petl/Helmet_blinker/Photos/IMG_20210405_172852.jpg

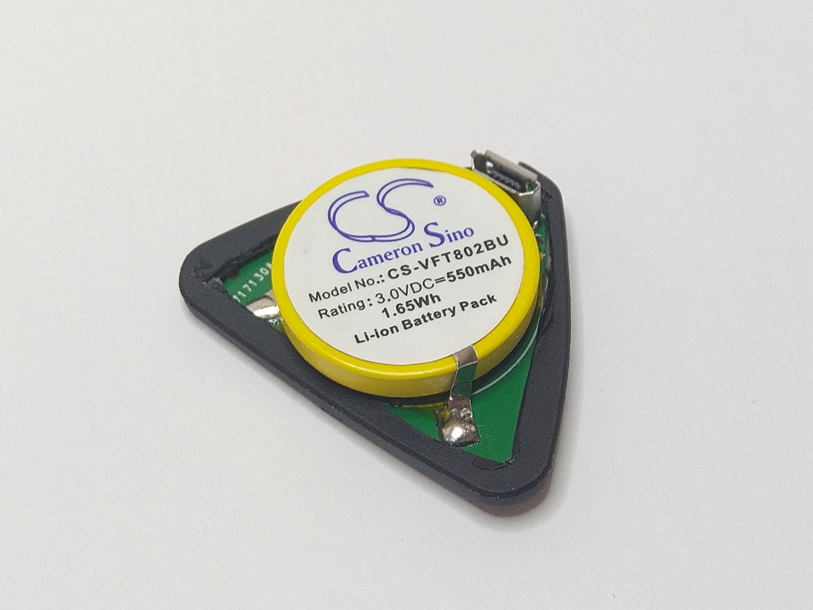
Photos/IMG_20210405_172852.jpg
