petl/Helmet_blinker/Photos/IMG_20210405_173359.jpg

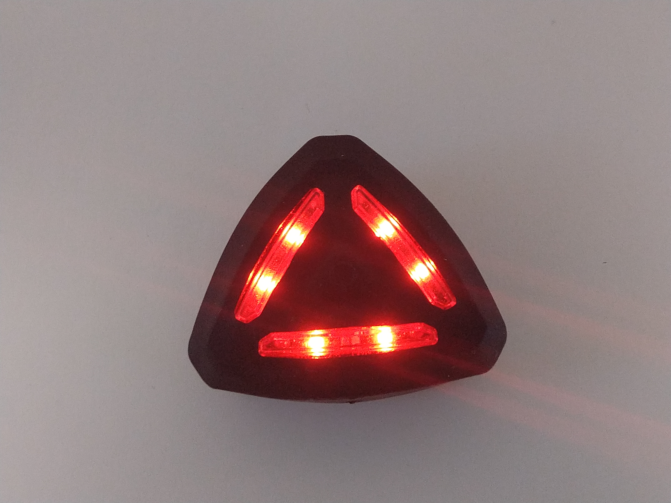
Photos/IMG_20210405_173359.jpg
