petl/Helmet_blinker/Photos/IMG_20210405_173910.jpg

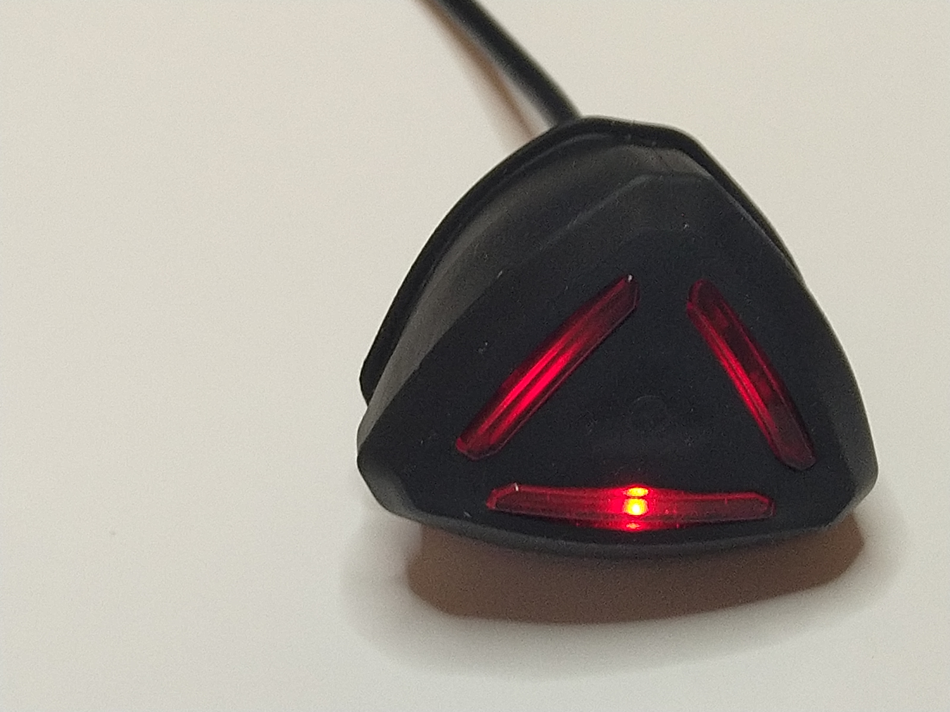
Photos/IMG_20210405_173910.jpg
