petl/Helmet_blinker/Photos/scaled/1.jpg

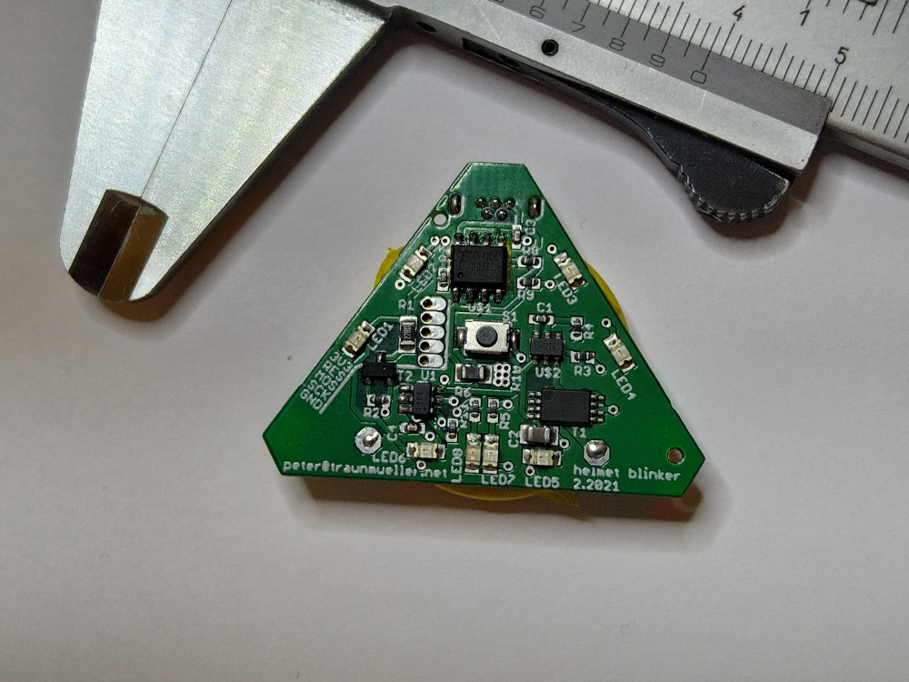
Photos/scaled/1.jpg
