petl/Helmet_blinker/Photos/scaled/3.jpg

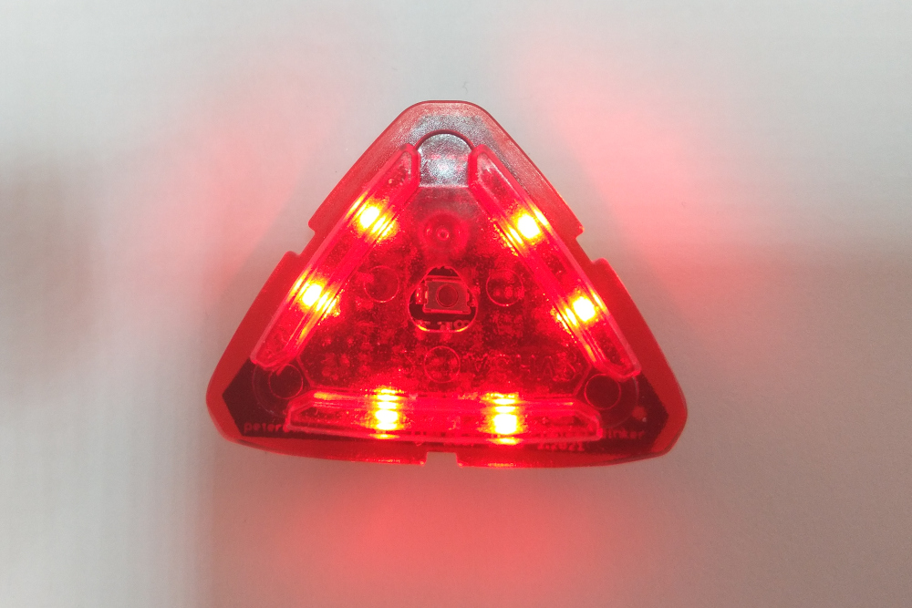
Photos/scaled/3.jpg
