petl/Helmet_blinker/Photos/scaled/5.jpg

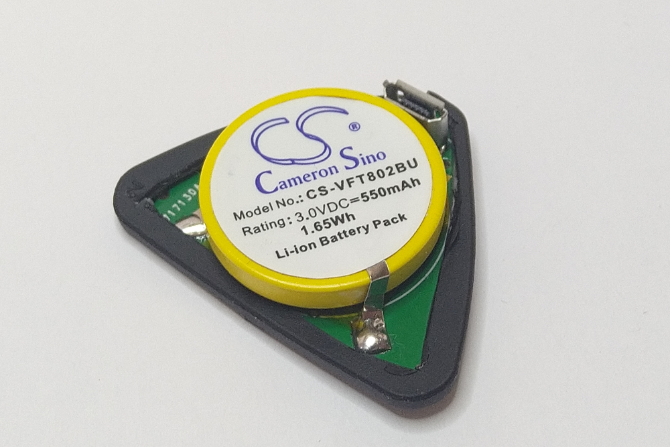
Photos/scaled/5.jpg
