petl/Helmet_blinker/Photos/scaled/6.jpg

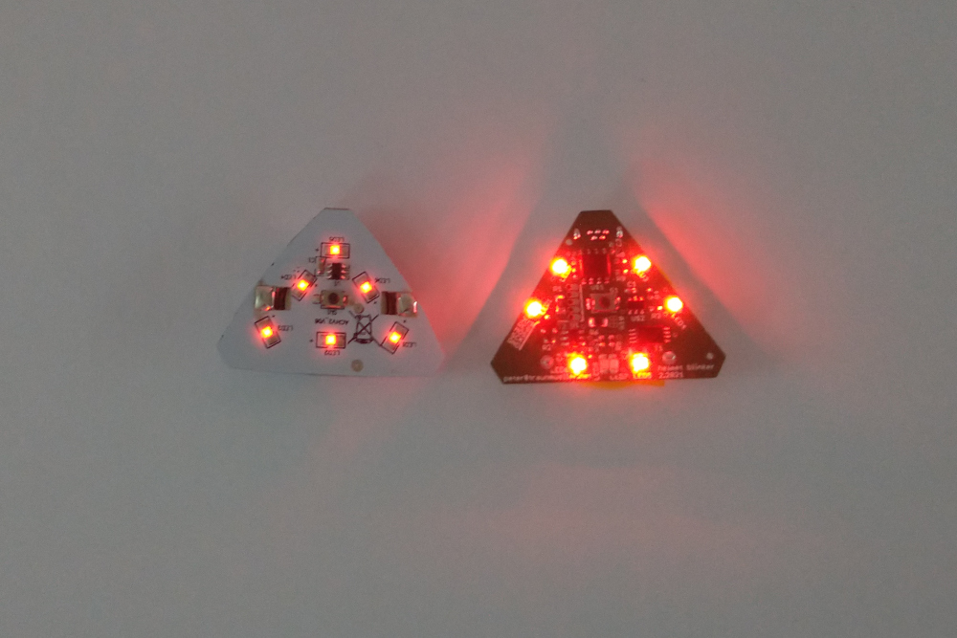
Photos/scaled/6.jpg
