petl/Helmet_blinker/Photos/scaled/IMG_20210405_172331_scaled.jpg

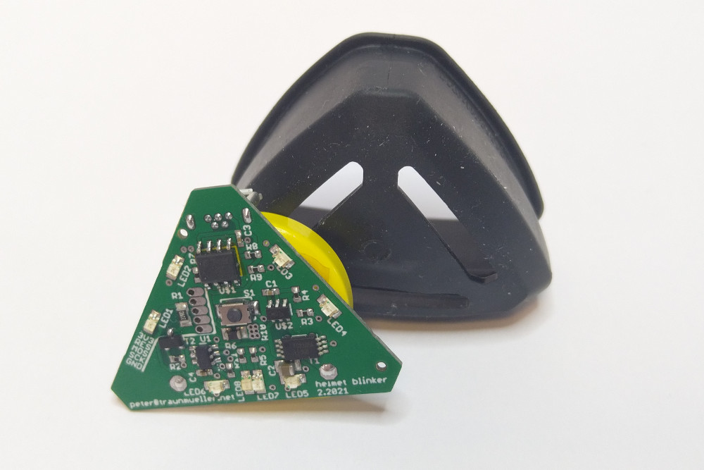
Photos/scaled/IMG_20210405_172331_scaled.jpg
