petl/Helmet_blinker/Photos/scaled/IMG_20210405_173359_scaled.jpg

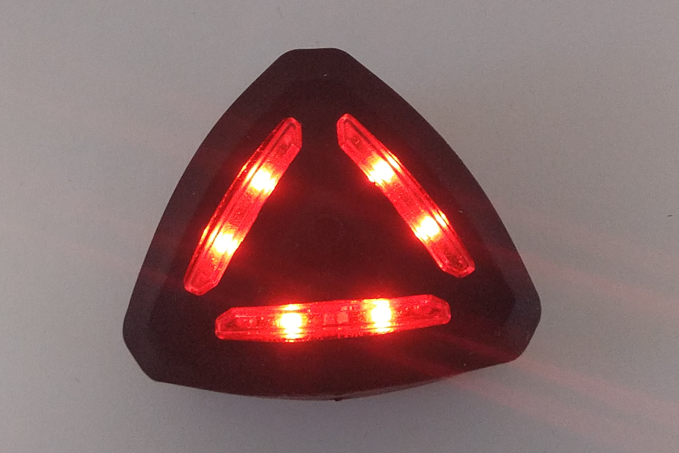
Photos/scaled/IMG_20210405_173359_scaled.jpg
